vill-jiang/uhf_recv/src/config.h

/*---------------------------------------------------------------------*/
/* --- STC MCU Limited ------------------------------------------------*/
/* --- STC 1T Series MCU Demo Programme -------------------------------*/
/* --- Mobile: (86)13922805190 ----------------------------------------*/
/* --- Fax: 86-0513-55012956,55012947,55012969 ------------------------*/
/* --- Tel: 86-0513-55012928,55012929,55012966 ------------------------*/
/* --- Web: www.STCAI.com ---------------------------------------------*/
/* --- BBS: www.STCAIMCU.com  -----------------------------------------*/
/* --- QQ:  800003751 -------------------------------------------------*/
/* 如果要在程序中使用此代码,请在程序中注明使用了STC的资料及程序            */
/*---------------------------------------------------------------------*/

#ifndef		__CONFIG_H__
#define		__CONFIG_H__

//========================================================================
//                               主时钟定义
//========================================================================

#ifdef F_CPU
#define MAIN_Fosc F_CPU
#else
#define MAIN_Fosc		24000000L	//定义主时钟
//#define MAIN_Fosc		22118400L	//定义主时钟
//#define MAIN_Fosc		12000000L	//定义主时钟
//#define MAIN_Fosc		11059200L	//定义主时钟
//#define MAIN_Fosc		 5529600L	//定义主时钟
#endif

//========================================================================
//                                头文件
//========================================================================

#include "type_def.h"
#include "STC8H.H"
// #include <intrins.h>
// #include <stdlib.h>
// #include <stdio.h>

//========================================================================
//                             引脚声明
//========================================================================

#define ENC_PIN_A P33  /* bit2: A相引脚 */
#define ENC_PIN_B P34  /* bit1: B相引脚 */
#define ENC_PIN_BTN P32  /* bit0: 按键引脚(E) */

#define KT0656M_CHIP_EN_AM P11
#define KT0656M_CHIP_EN_BM P12
#define PCM_MUTE_PIN P13
#define WS2812_PIN P10

#endif
