vill-jiang/uhf_recv/src/type_def.h

/*---------------------------------------------------------------------*/
/* --- STC MCU Limited ------------------------------------------------*/
/* --- STC 1T Series MCU Demo Programme -------------------------------*/
/* --- Mobile: (86)13922805190 ----------------------------------------*/
/* --- Fax: 86-0513-55012956,55012947,55012969 ------------------------*/
/* --- Tel: 86-0513-55012928,55012929,55012966 ------------------------*/
/* --- Web: www.STCAI.com ---------------------------------------------*/
/* --- BBS: www.STCAIMCU.com  -----------------------------------------*/
/* --- QQ:  800003751 -------------------------------------------------*/
/* 如果要在程序中使用此代码,请在程序中注明使用了STC的资料及程序            */
/*---------------------------------------------------------------------*/

#ifndef		__TYPE_DEF_H
#define		__TYPE_DEF_H

//========================================================================
//                               类型定义
//========================================================================

typedef signed char     int8_t;   //  8 bits 
typedef signed int      int16_t;  // 16 bits 
typedef signed long     int32_t;  // 32 bits 

typedef unsigned char   uint8_t;  //  8 bits 
typedef unsigned int    uint16_t; // 16 bits 
typedef unsigned long   uint32_t; // 32 bits 
typedef unsigned char   bool;  //  8 bits 

//===================================================

#define	TRUE	1
#define	FALSE	0

//===================================================

#define	NULL	0

//===================================================

#define	Priority_0			0	//中断优先级为 0 级（最低级）
#define	Priority_1			1	//中断优先级为 1 级（较低级）
#define	Priority_2			2	//中断优先级为 2 级（较高级）
#define	Priority_3			3	//中断优先级为 3 级（最高级）

#define ENABLE		1
#define DISABLE		0

#define SUCCESS		0
#define FAIL		-1

//===================================================

#define	I2C_Mode_Master			1
#define	I2C_Mode_Slave			0

#define	PIE			0x20	//1: 比较结果由0变1, 产生上升沿中断
#define	NIE			0x10	//1: 比较结果由1变0, 产生下降沿中断

#define	PWMA	128
#define	PWMB	129

//===================================================

#endif
