vill-jiang/uhf_recv/src/STC8G_H_EEPROM.h

/*---------------------------------------------------------------------*/
/* --- STC MCU Limited ------------------------------------------------*/
/* --- STC 1T Series MCU Demo Programme -------------------------------*/
/* --- Mobile: (86)13922805190 ----------------------------------------*/
/* --- Fax: 86-0513-55012956,55012947,55012969 ------------------------*/
/* --- Tel: 86-0513-55012928,55012929,55012966 ------------------------*/
/* --- Web: www.STCAI.com ---------------------------------------------*/
/* --- BBS: www.STCAIMCU.com  -----------------------------------------*/
/* --- QQ:  800003751 -------------------------------------------------*/
/* 如果要在程序中使用此代码,请在程序中注明使用了STC的资料及程序            */
/*---------------------------------------------------------------------*/

#ifndef	__STC8G_H_EEPROM_H
#define	__STC8G_H_EEPROM_H

#include	"config.h"

// 大约277Byte的代码体积
#define USE_EEPROM

//	选择MCU型号
// #define	MCU_Type	STC8X1K08  //STC8X1K08, STC8X1K16, STC8XxK32, STC8XxK32, STC8XxK60

/************************** ISP/IAP *****************************

   型号    大小  扇区数  开始地址    结束地址   MOVC读偏移地址
STC8X1K08   4K   8扇区   0x0000  ~  0x0FFF       0x2000
STC8X1K16  12K   24扇区  0x0000  ~  0x2FFF       0x4000
STC8XxK32  32K   64扇区  0x0000  ~  0x7FFF       0x8000
STC8XxK60   4K   8扇区   0x0000  ~  0x0FFF       0xF000

*/

// STC8X1K17 预留 4K EEPROM
#define MOVC_ShiftAddress 0x3400

//========================================================================
//                               IAP设置
//========================================================================
#ifdef USE_EEPROM
//sfr IAP_CMD   = 0xC5;
#define		IAP_STANDBY()	IAP_CMD = 0		//IAP空闲命令（禁止）
#define		IAP_READ()		IAP_CMD = 1		//IAP读出命令
#define		IAP_WRITE()		IAP_CMD = 2		//IAP写入命令
#define		IAP_ERASE()		IAP_CMD = 3		//IAP擦除命令

//sfr IAP_TRIG  = 0xC6;
#define 	IAP_TRIG()	IAP_TRIG = 0x5A,	IAP_TRIG = 0xA5		/* IAP触发命令 */

//							            7    6    5      4    3   2  1   0   Reset Value
//sfr IAP_CONTR = 0xC7;		IAPEN SWBS SWRST CFAIL  -   -  -   -   0000,x000	//IAP Control Register
#define IAP_EN          (1<<7)
#define IAP_SWBS        (1<<6)
#define IAP_SWRST       (1<<5)
#define IAP_CMD_FAIL    (1<<4)

#define	IAP_ENABLE()		IAP_CONTR = IAP_EN; IAP_TPS = MAIN_Fosc / 1000000L
#define	IAP_DISABLE()		IAP_CONTR = 0; IAP_CMD = 0; IAP_TRIG = 0; IAP_ADDRH = 0xff; IAP_ADDRL = 0xff

//========================================================================
//                              定义声明
//========================================================================

#define		STC8X1K08	8
#define		STC8X1K16	16
#define		STC8XxK32	32
#define		STC8XxK60	60


void	DisableEEPROM(void);
void 	EEPROM_read_n(uint16_t EE_address,uint8_t *DataAddress,uint16_t number);
void 	EEPROM_write_n(uint16_t EE_address,uint8_t *DataAddress,uint16_t number);
void	EEPROM_SectorErase(uint16_t EE_address);
#endif


#endif
