vill-jiang/uhf_recv/src/STC8G_H_Timer_Isr.c

/*---------------------------------------------------------------------*/
/* --- STC MCU Limited ------------------------------------------------*/
/* --- STC 1T Series MCU Demo Programme -------------------------------*/
/* --- Mobile: (86)13922805190 ----------------------------------------*/
/* --- Fax: 86-0513-55012956,55012947,55012969 ------------------------*/
/* --- Tel: 86-0513-55012928,55012929,55012966 ------------------------*/
/* --- Web: www.STCAI.com ---------------------------------------------*/
/* --- BBS: www.STCAIMCU.com  -----------------------------------------*/
/* --- QQ:  800003751 -------------------------------------------------*/
/* 如果要在程序中使用此代码,请在程序中注明使用了STC的资料及程序            */
/*---------------------------------------------------------------------*/

#include	"STC8G_H_Timer.h"

//========================================================================
// 函数: Timer0_ISR_Handler
// 描述: Timer0中断函数.
// 参数: none.
// 返回: none.
// 版本: V1.0, 2020-09-23
//========================================================================
// #ifdef Timer0 在编码器中定义
// INTERRUPT(Timer0_ISR_Handler, TMR0_VECTOR)		//进中断时已经清除标志
// {
// 	// TODO: 在此处添加用户代码
//    P67 = ! P67;
// }
// #endif

//========================================================================
// 函数: Timer1_ISR_Handler
// 描述: Timer1中断函数.
// 参数: none.
// 返回: none.
// 版本: V1.0, 2020-09-23
//========================================================================
#ifdef Timer1
INTERRUPT(Timer1_ISR_Handler, TMR1_VECTOR)		//进中断时已经清除标志
{
	// TODO: 在此处添加用户代码
   P66 = ! P66;
}
#endif

//========================================================================
// 函数: Timer2_ISR_Handler
// 描述: Timer2中断函数.
// 参数: none.
// 返回: none.
// 版本: V1.0, 2020-09-23
//========================================================================
#ifdef Timer2
INTERRUPT(Timer2_ISR_Handler, TMR2_VECTOR)		//进中断时已经清除标志
{
	// TODO: 在此处添加用户代码
   P65 = ! P65;
}
#endif

//========================================================================
// 函数: Timer3_ISR_Handler
// 描述: Timer3中断函数.
// 参数: none.
// 返回: none.
// 版本: V1.0, 2020-09-23
//========================================================================
#ifdef Timer3
INTERRUPT(Timer3_ISR_Handler, TMR3_VECTOR)		//进中断时已经清除标志
{
	// TODO: 在此处添加用户代码
	P64 = ! P64;
}
#endif

//========================================================================
// 函数: Timer4_ISR_Handler
// 描述: Timer4中断函数.
// 参数: none.
// 返回: none.
// 版本: V1.0, 2020-09-23
//========================================================================
#ifdef Timer4
INTERRUPT(Timer4_ISR_Handler, TMR4_VECTOR)		//进中断时已经清除标志
{
	// TODO: 在此处添加用户代码
	P63 = ! P63;
}
#endif
